rimuadmin/TeensyMaestro-Hardware/images/3.5mm_trs_plug.png

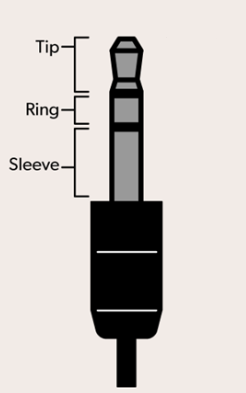
images/3.5mm_trs_plug.png
