rimuadmin/TeensyMaestro-Hardware/images/front_panel_with_encoders.jpg

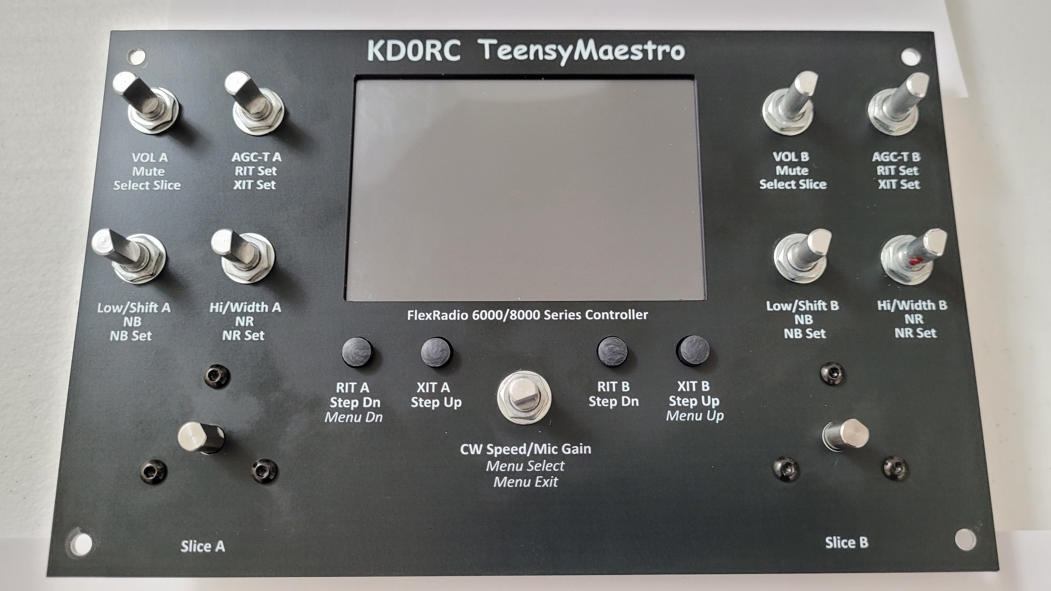
images/front_panel_with_encoders.jpg
