rimuadmin/TeensyMaestro-Hardware/images/large_encoder_plugin.jpg

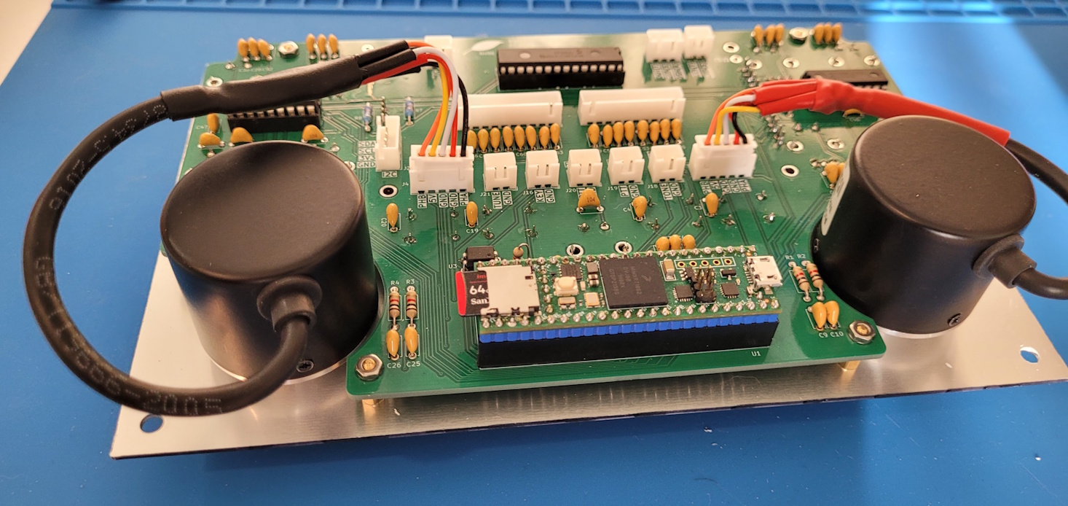
images/large_encoder_plugin.jpg
