rimuadmin/TeensyMaestro-Hardware/images/lcd_teensy_maestro_connected.jpg

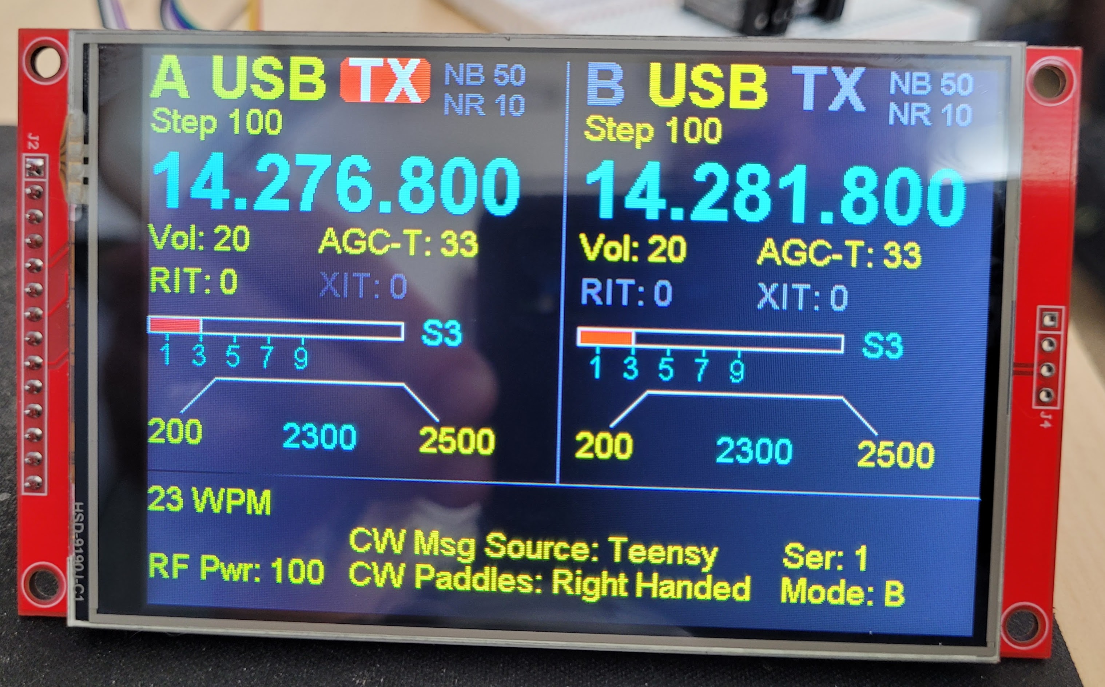
images/lcd_teensy_maestro_connected.jpg
