rimuadmin/TeensyMaestro-Hardware/images/mcp23008_socket_positions.png

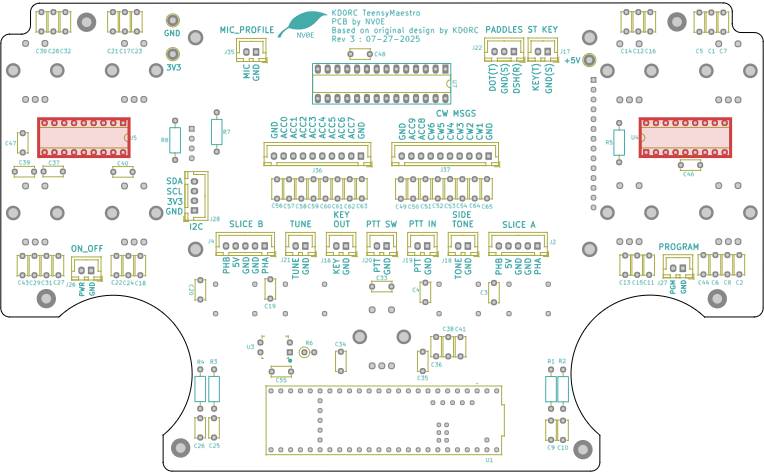
images/mcp23008_socket_positions.png
