rimuadmin/TeensyMaestro-Hardware/images/mcp23017_indent_position.jpg

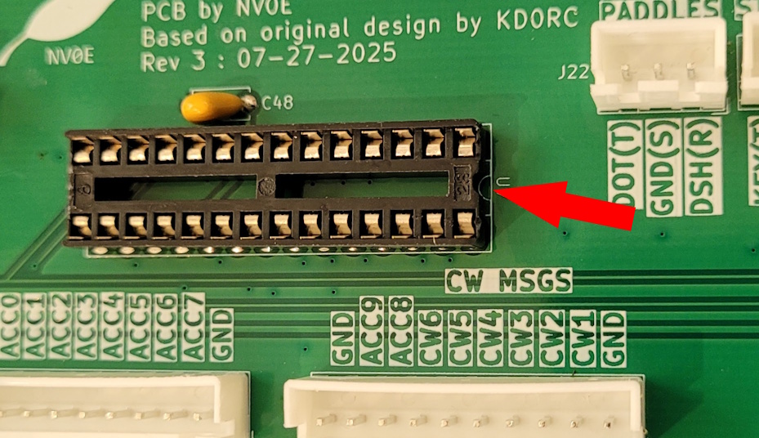
images/mcp23017_indent_position.jpg
