rimuadmin/TeensyMaestro-Hardware/images/opto_isolator_position.jpg

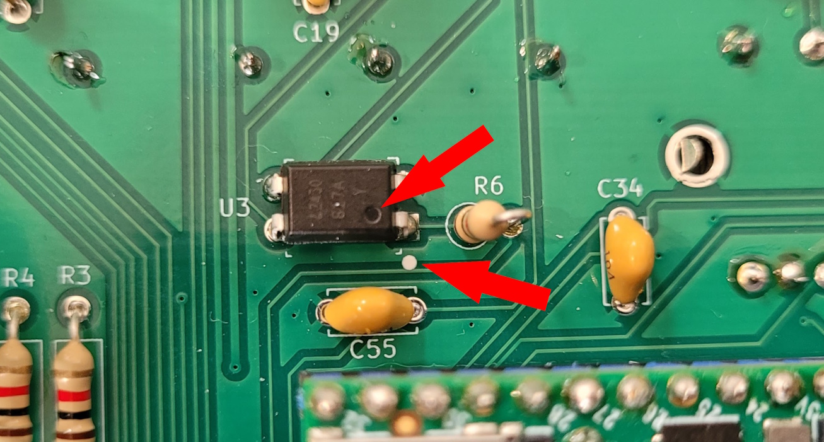
images/opto_isolator_position.jpg
