rimuadmin/TeensyMaestro-Hardware/images/pcb_rear_with_ics.jpg

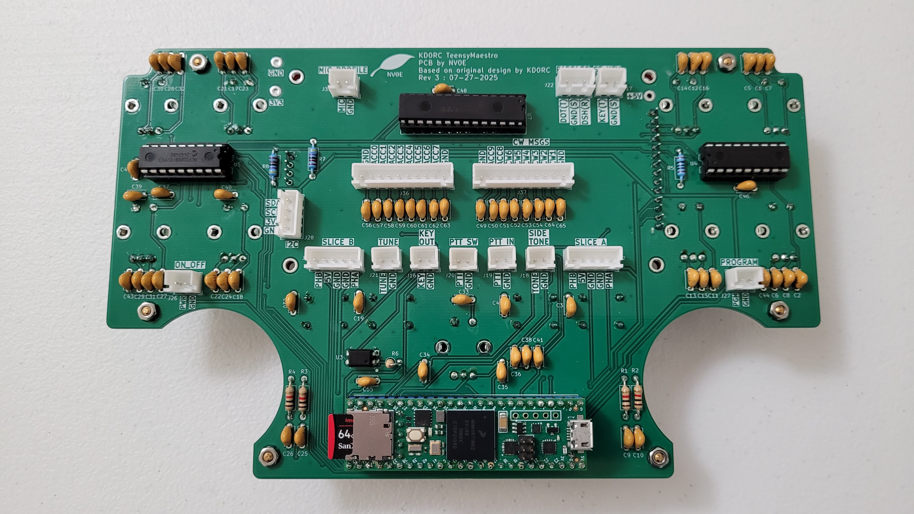
images/pcb_rear_with_ics.jpg
