rimuadmin/TeensyMaestro-Hardware/images/pcb_sockets_caps.jpg

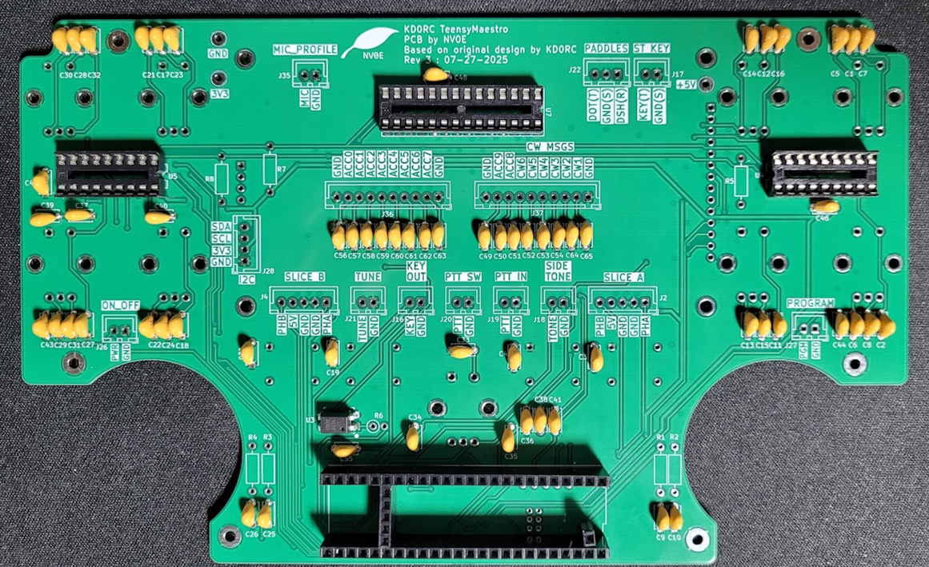
images/pcb_sockets_caps.jpg
