rimuadmin/TeensyMaestro-Hardware/images/pcb_sockets_opto.jpg

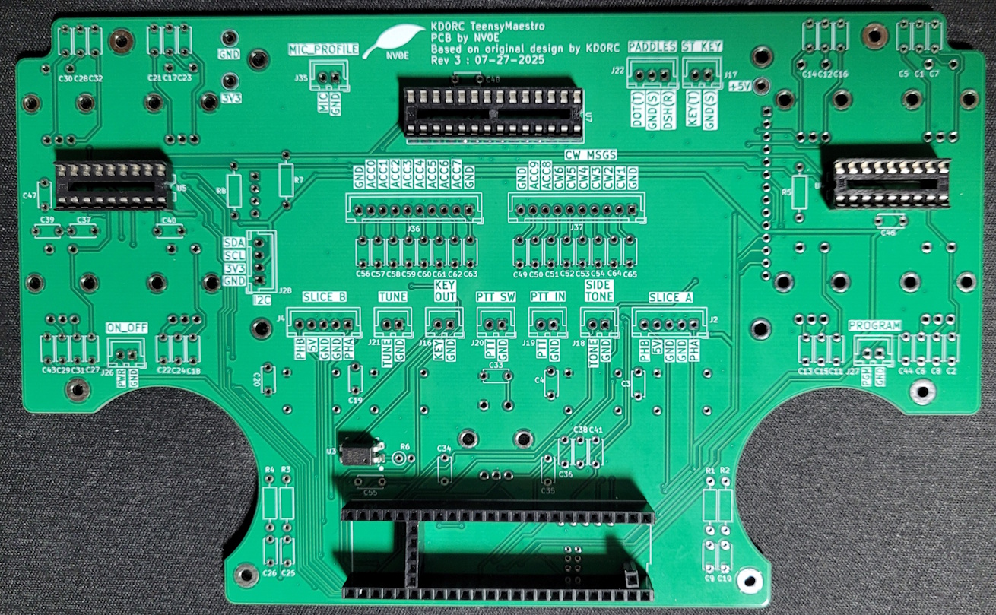
images/pcb_sockets_opto.jpg
