rimuadmin/TeensyMaestro-Hardware/images/PCB_standoffs.jpg

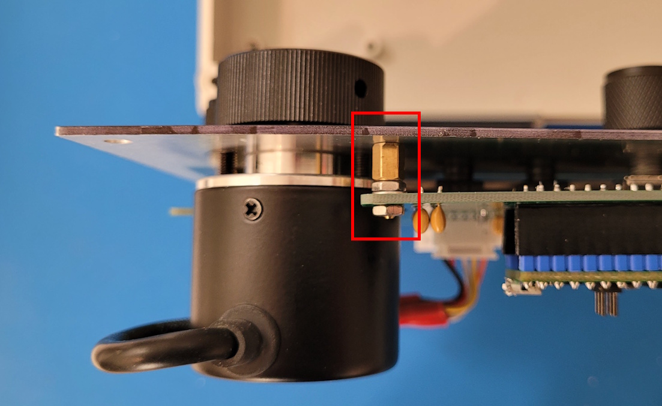
images/PCB_standoffs.jpg
