rimuadmin/TeensyMaestro-Hardware/images/push_button_positions.png

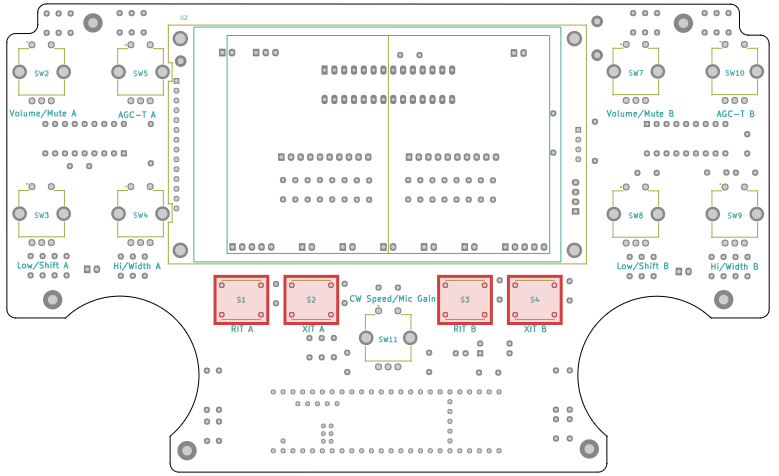
images/push_button_positions.png
