rimuadmin/TeensyMaestro-Hardware/images/rear_enclosure_panel.jpg

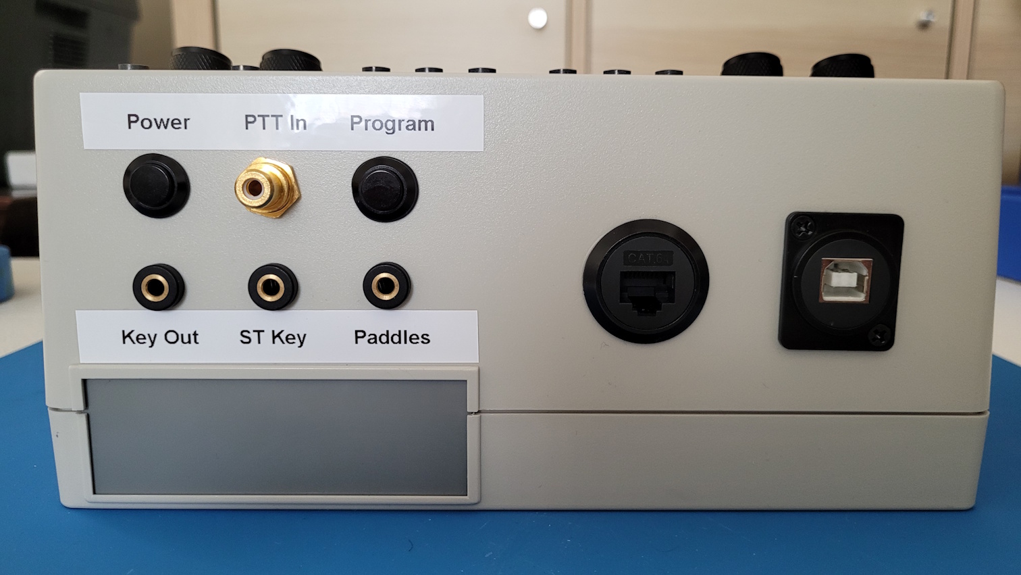
images/rear_enclosure_panel.jpg
