rimuadmin/TeensyMaestro-Hardware/images/rear_enclosure_panel_50.jpg

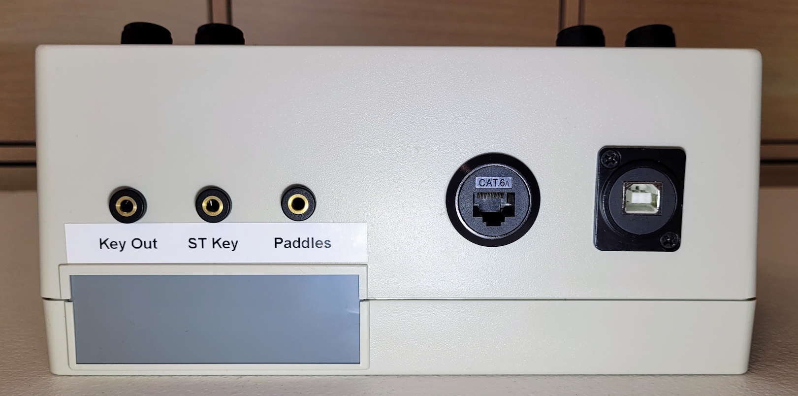
images/rear_enclosure_panel_50.jpg
