rimuadmin/TeensyMaestro-Hardware/images/rear_side_2025-08-06.png

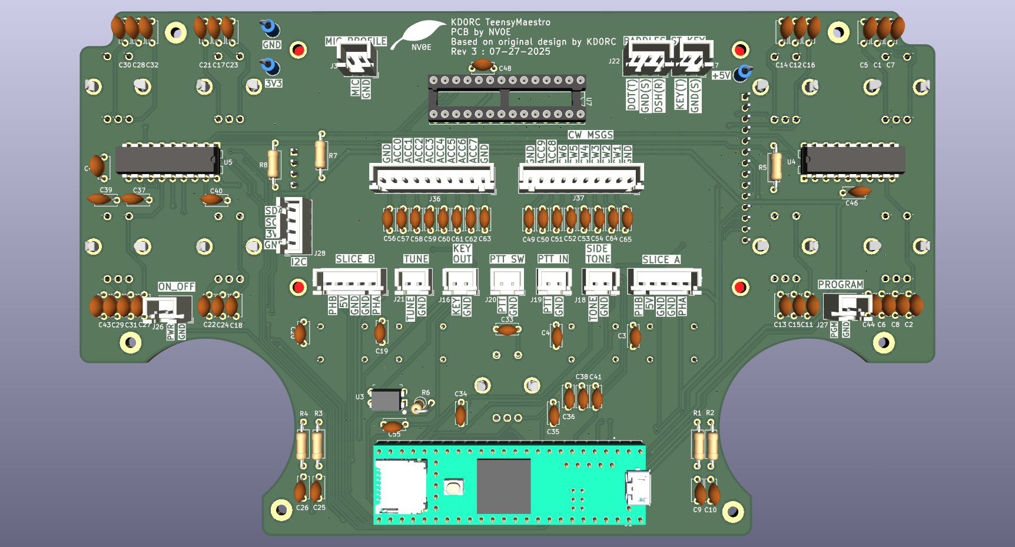
images/rear_side_2025-08-06.png
