rimuadmin/TeensyMaestro-Hardware/images/resistor-1k-positions.png

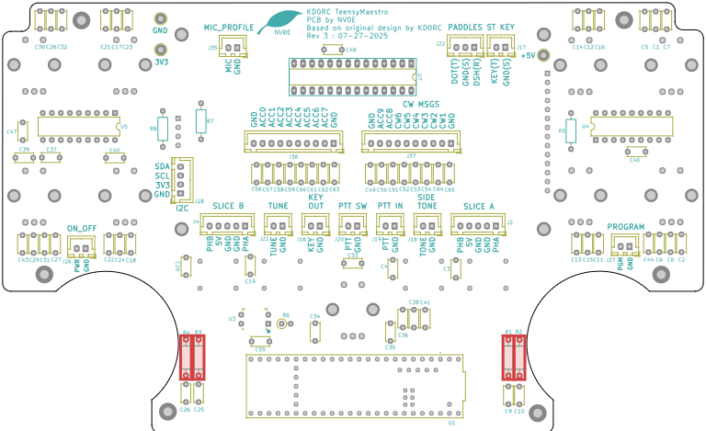
images/resistor-1k-positions.png
