rimuadmin/TeensyMaestro-Hardware/images/resistor-1k-vert-positions.png

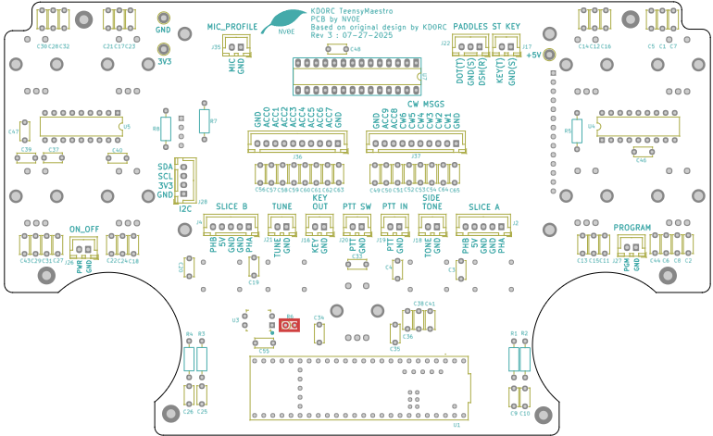
images/resistor-1k-vert-positions.png
