rimuadmin/TeensyMaestro-Hardware/images/resistor-4k7-positions.png

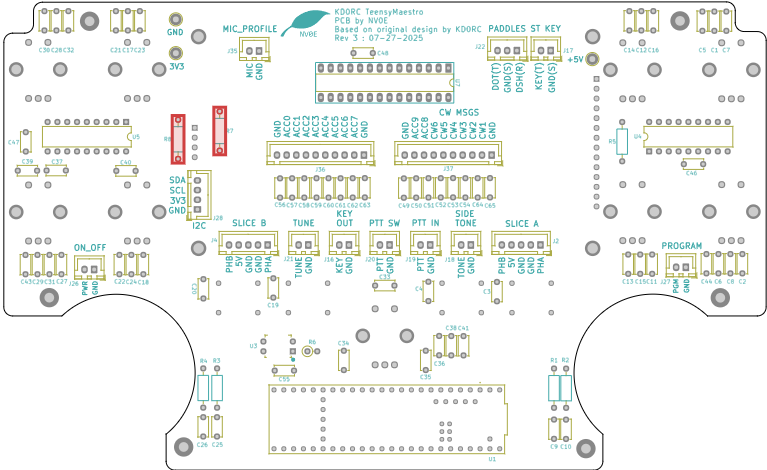
images/resistor-4k7-positions.png
