rimuadmin/TeensyMaestro-Hardware/images/resistor-100R-position.png

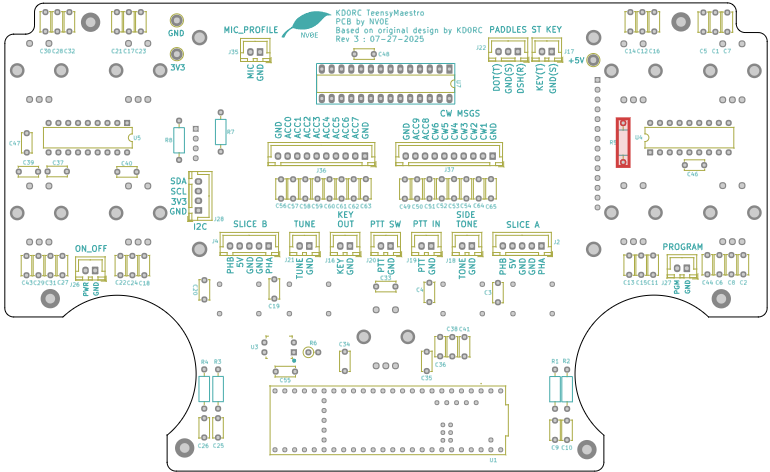
images/resistor-100R-position.png
