rimuadmin/TeensyMaestro-Hardware/images/small_encoder_positions.png

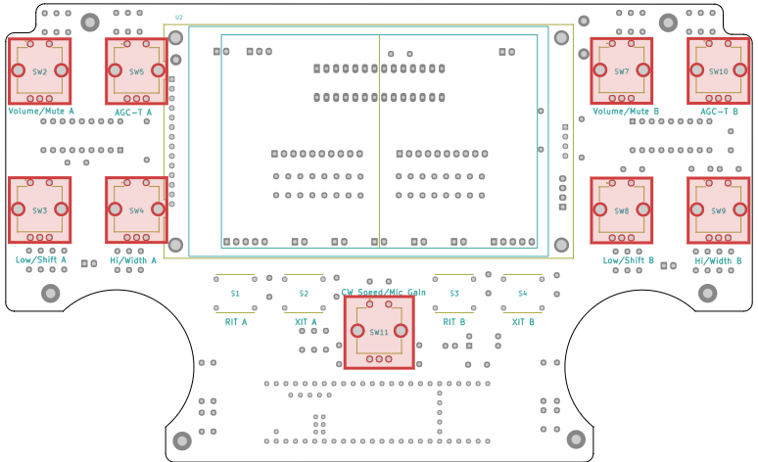
images/small_encoder_positions.png
