rimuadmin/TeensyMaestro-Hardware/images/socket_18_pin.jpg

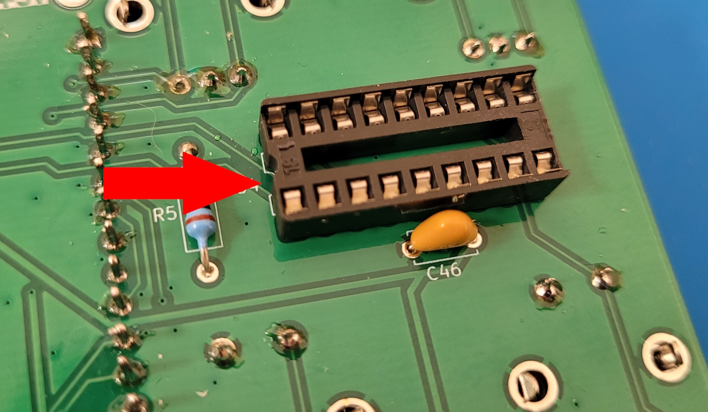
images/socket_18_pin.jpg
