rimuadmin/TeensyMaestro-Hardware/images/standoff_size.jpg

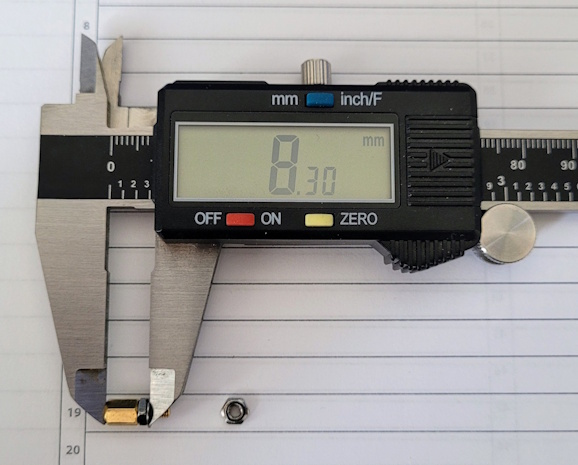
images/standoff_size.jpg
