rimuadmin/TeensyMaestro-Hardware/images/teensy4.1_ethernet.jpg

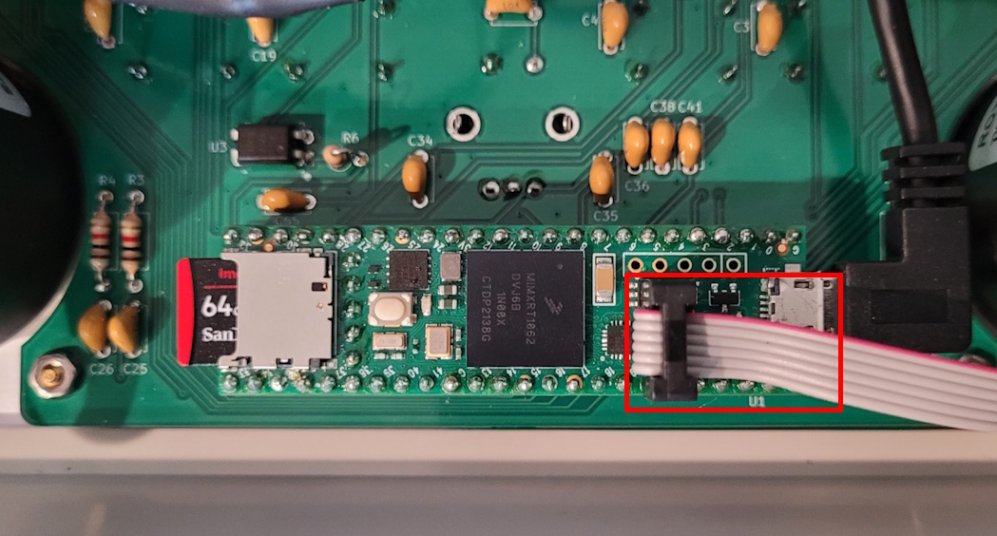
images/teensy4.1_ethernet.jpg
