rimuadmin/TeensyMaestro-Hardware/images/Teensy4.1_female_headers.jpg

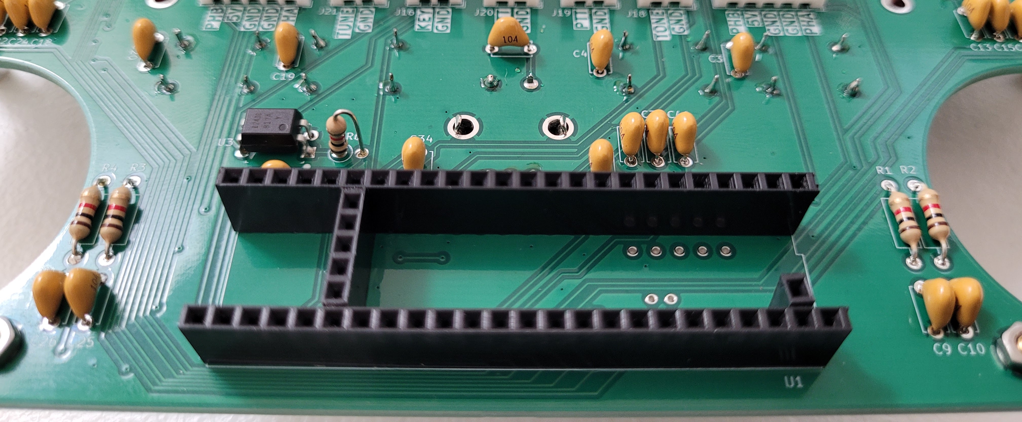
images/Teensy4.1_female_headers.jpg
