rimuadmin/TeensyMaestro-Hardware/images/teensy4.1_magjack.jpg

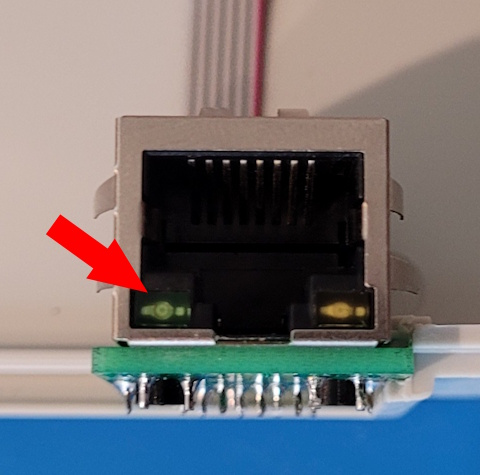
images/teensy4.1_magjack.jpg
