rimuadmin/TeensyMaestro-Hardware/images/Teensy4.1_with_pins.jpg

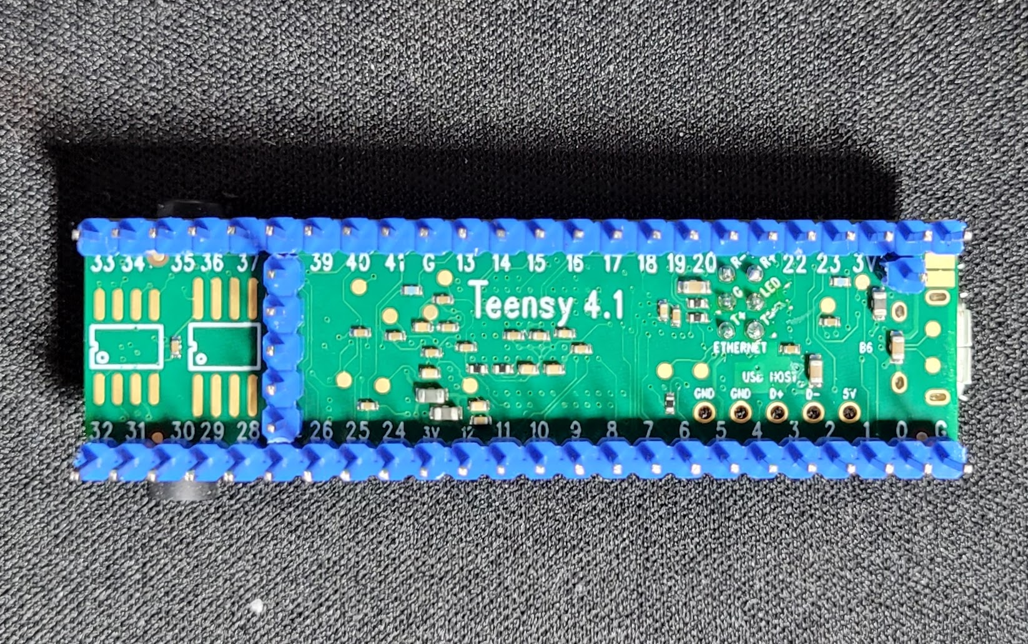
images/Teensy4.1_with_pins.jpg
