rimuadmin/TeensyMaestro-Hardware/images/teensy_maestro_enclosure_mounting.jpg

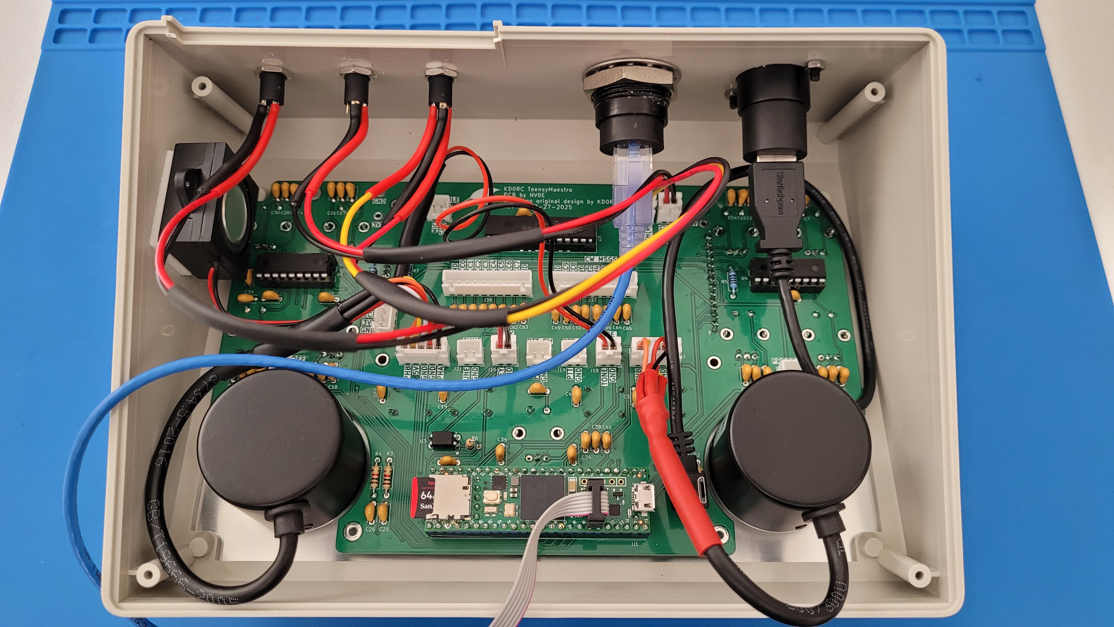
images/teensy_maestro_enclosure_mounting.jpg
