rimuadmin/TeensyMaestro-Hardware/images/TeensyMaestro_complete.jpg

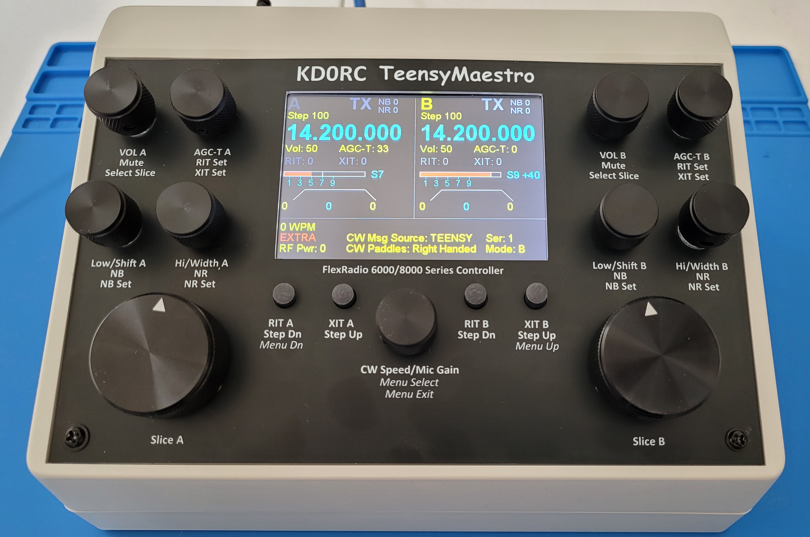
images/TeensyMaestro_complete.jpg
