rimuadmin/TeensyMaestro-Hardware/images/TeensyMaestro_front_panel_black-rev3.png

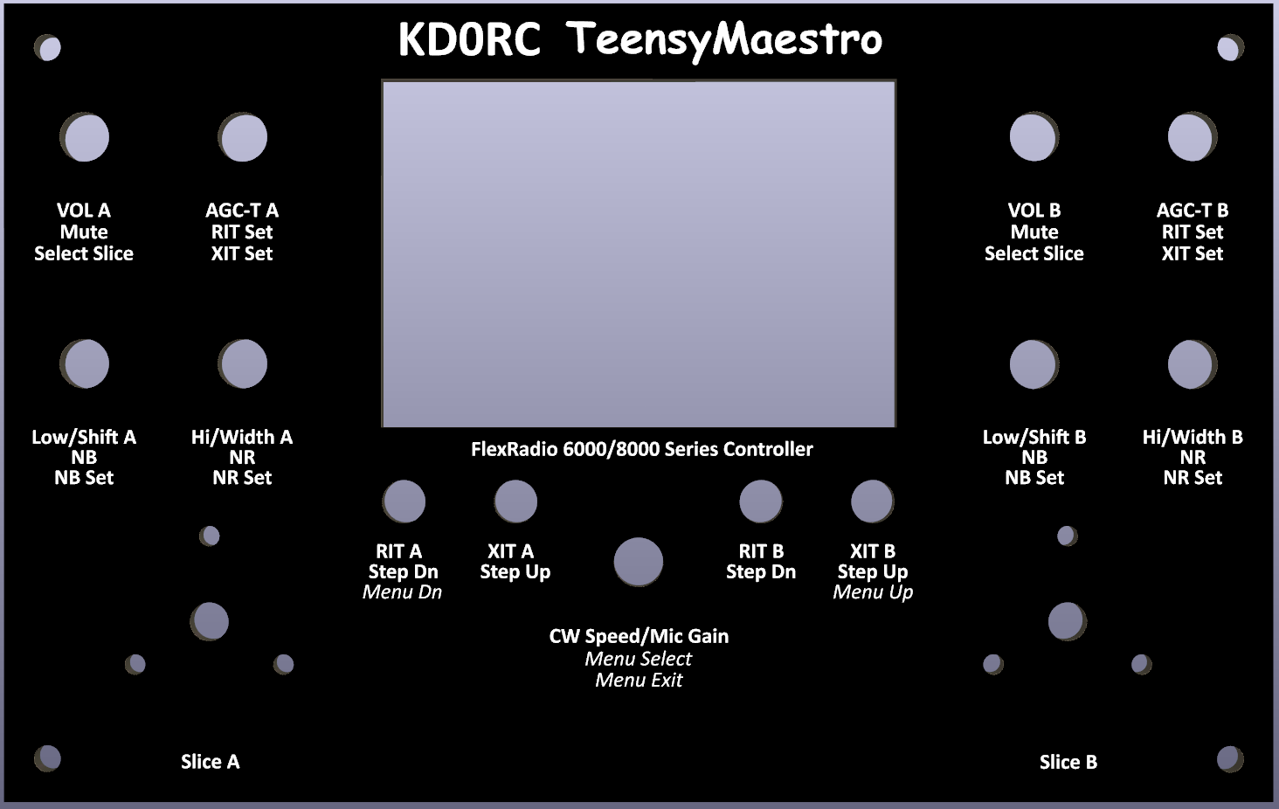
images/TeensyMaestro_front_panel_black-rev3.png
