rimuadmin/TeensyMaestro-Hardware/images/TeensyMaestro_pcb_front_20250806.jpg

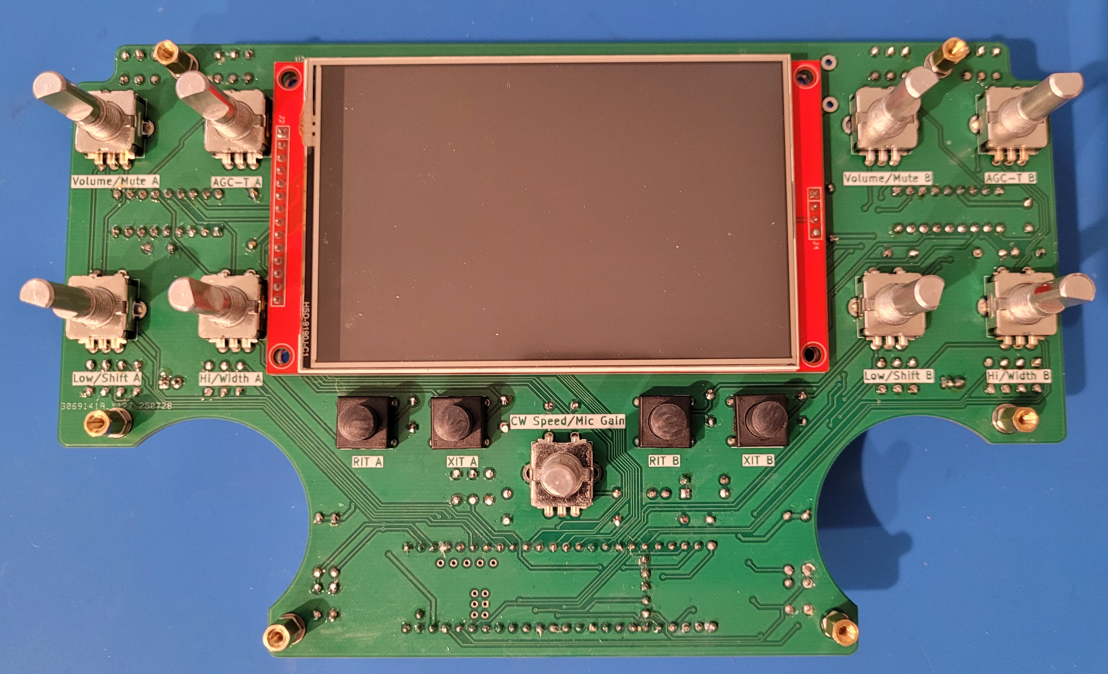
images/TeensyMaestro_pcb_front_20250806.jpg
