rimuadmin/TeensyMaestro-Hardware/images/tft_display_rear.png

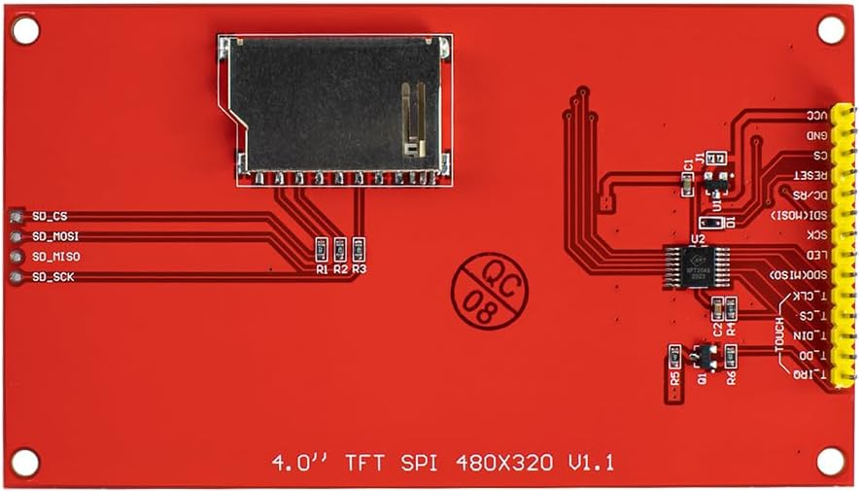
images/tft_display_rear.png
