rimuadmin/TeensyMaestro-Hardware/images/tft_sd_card_removal.jpg

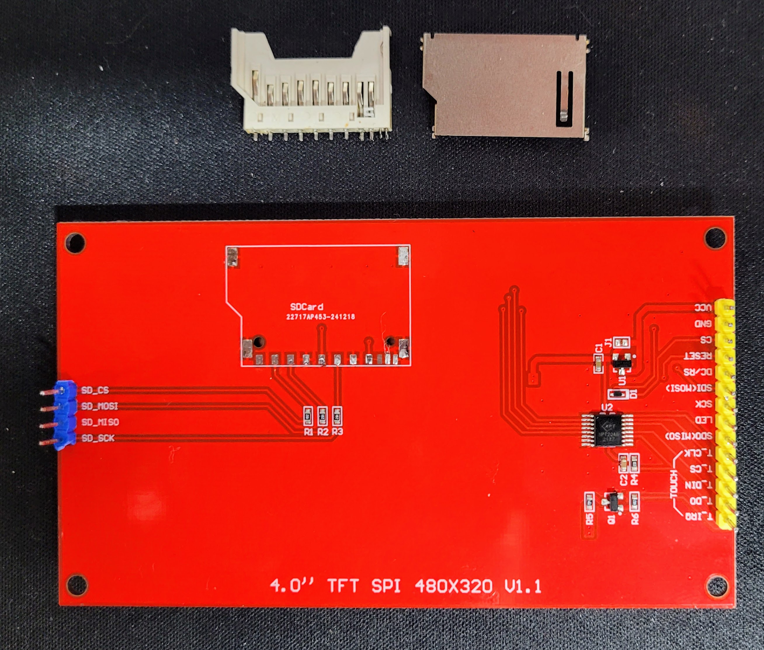
images/tft_sd_card_removal.jpg
