rimuadmin/TeensyMaestro-Hardware/images/USB-LH-Connector.jpg

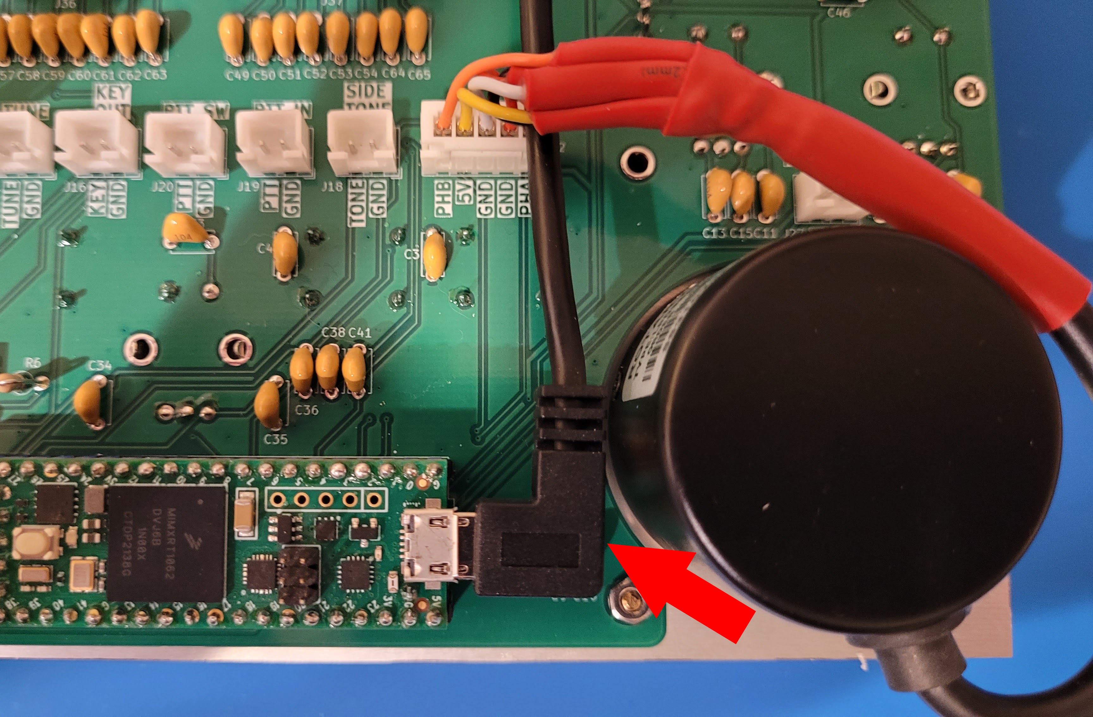
images/USB-LH-Connector.jpg
