rimuadmin/TeensyMaestro-Hardware/images/USB-Type-A_to_USB-B.png

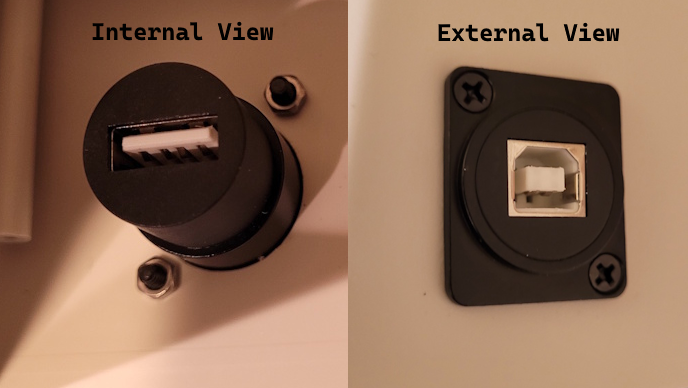
images/USB-Type-A_to_USB-B.png
