rimuadmin/TeensyMaestro-Hardware/images/XH_2-pin_connectors.png

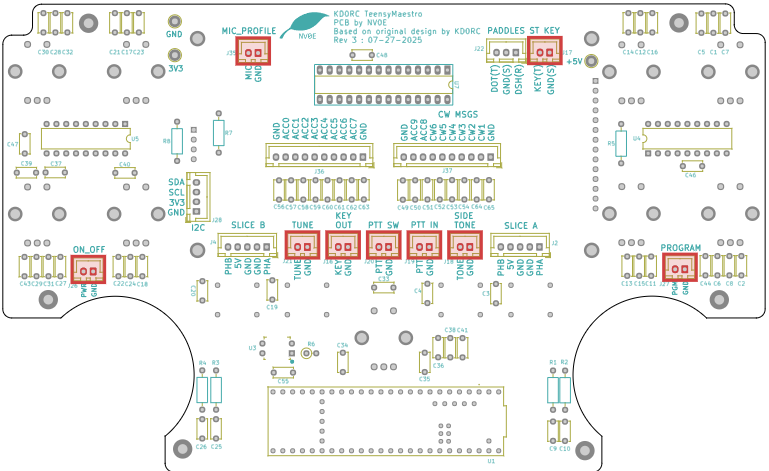
images/XH_2-pin_connectors.png
