rimuadmin/TeensyMaestro-Hardware/images/XH_4-pin_connector.png

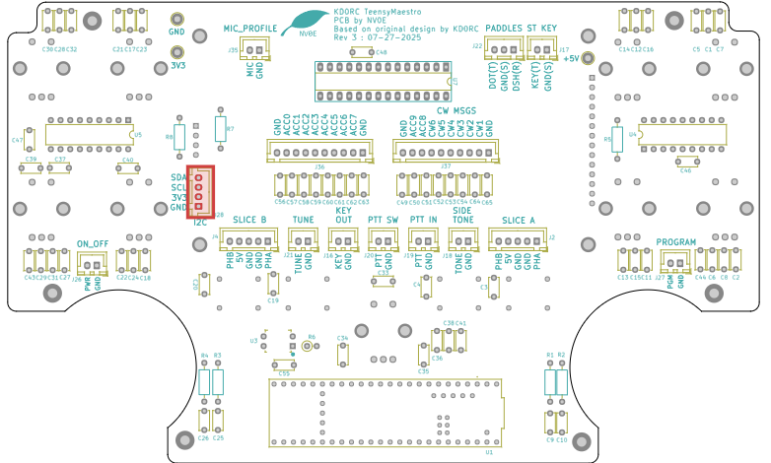
images/XH_4-pin_connector.png
