rimuadmin/TeensyMaestro-Hardware/images/XH_5-pin_connector.png

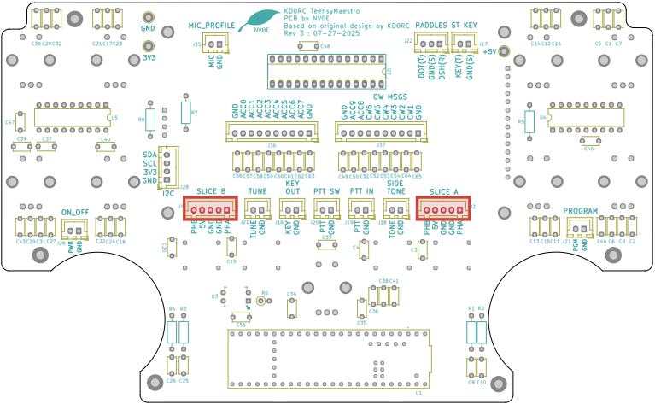
images/XH_5-pin_connector.png
