rimuadmin/TeensyMaestro-Hardware/images/tft_display_rear_parts_desolder_2.png

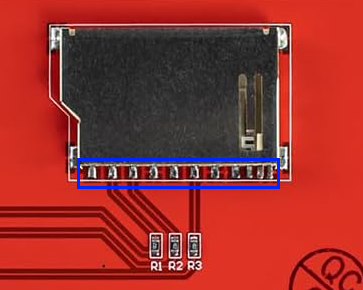
images/tft_display_rear_parts_desolder_2.png
