rimuadmin/TeensyMaestro-Hardware/images/teensy_maestro_assembled_front.jpg

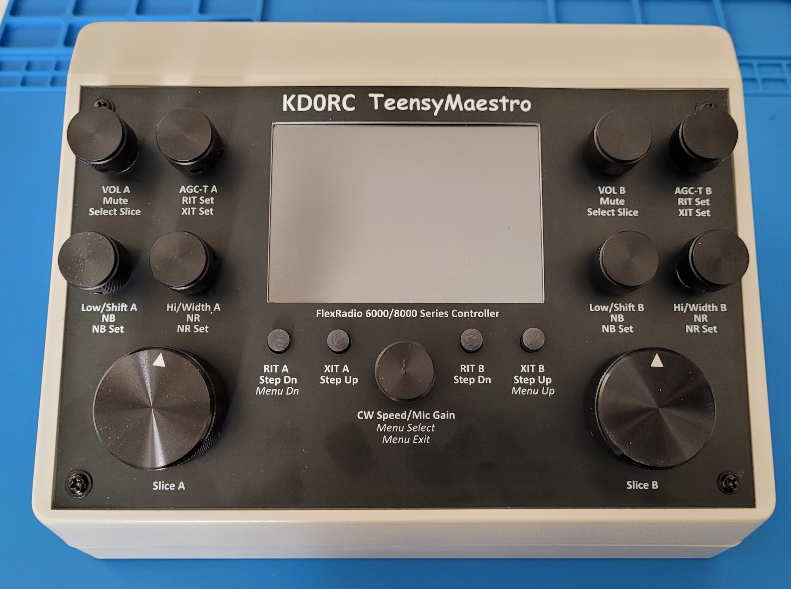
images/teensy_maestro_assembled_front.jpg
