rimuadmin/TeensyMaestro-Hardware/images/teensymaestro_assembled_202509.jpg

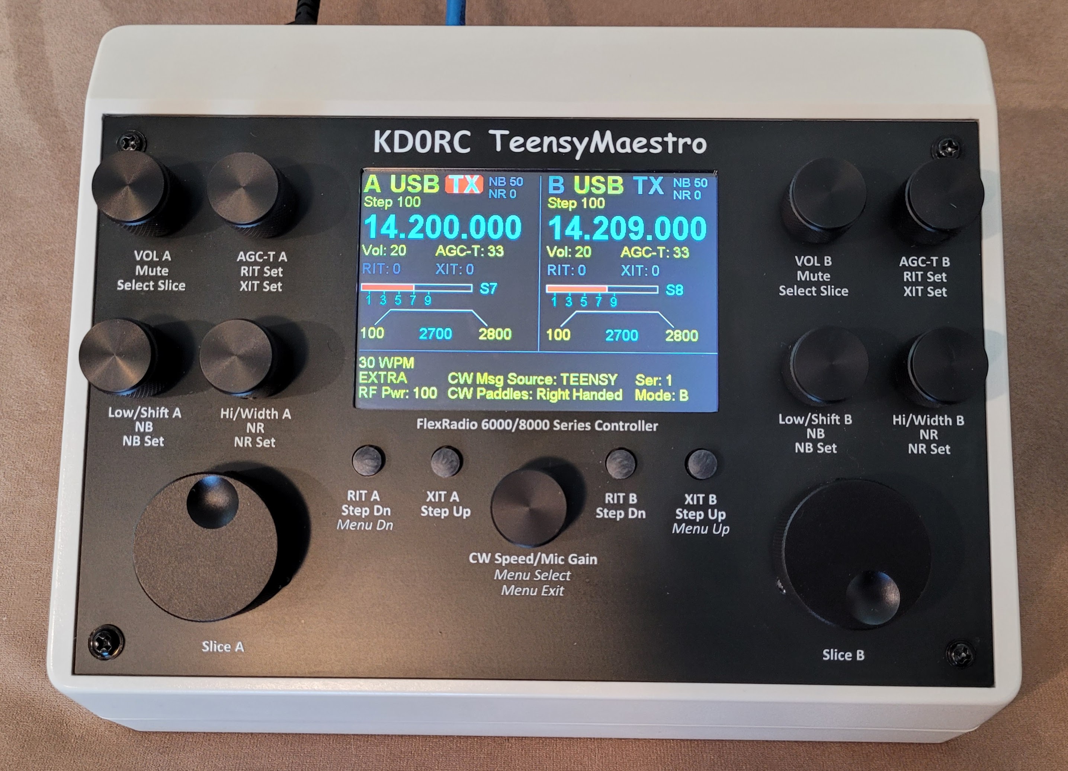
images/teensymaestro_assembled_202509.jpg
